Coolbots7/development-boards/atmega32u4_dev_board/images/layout/top_filled.png

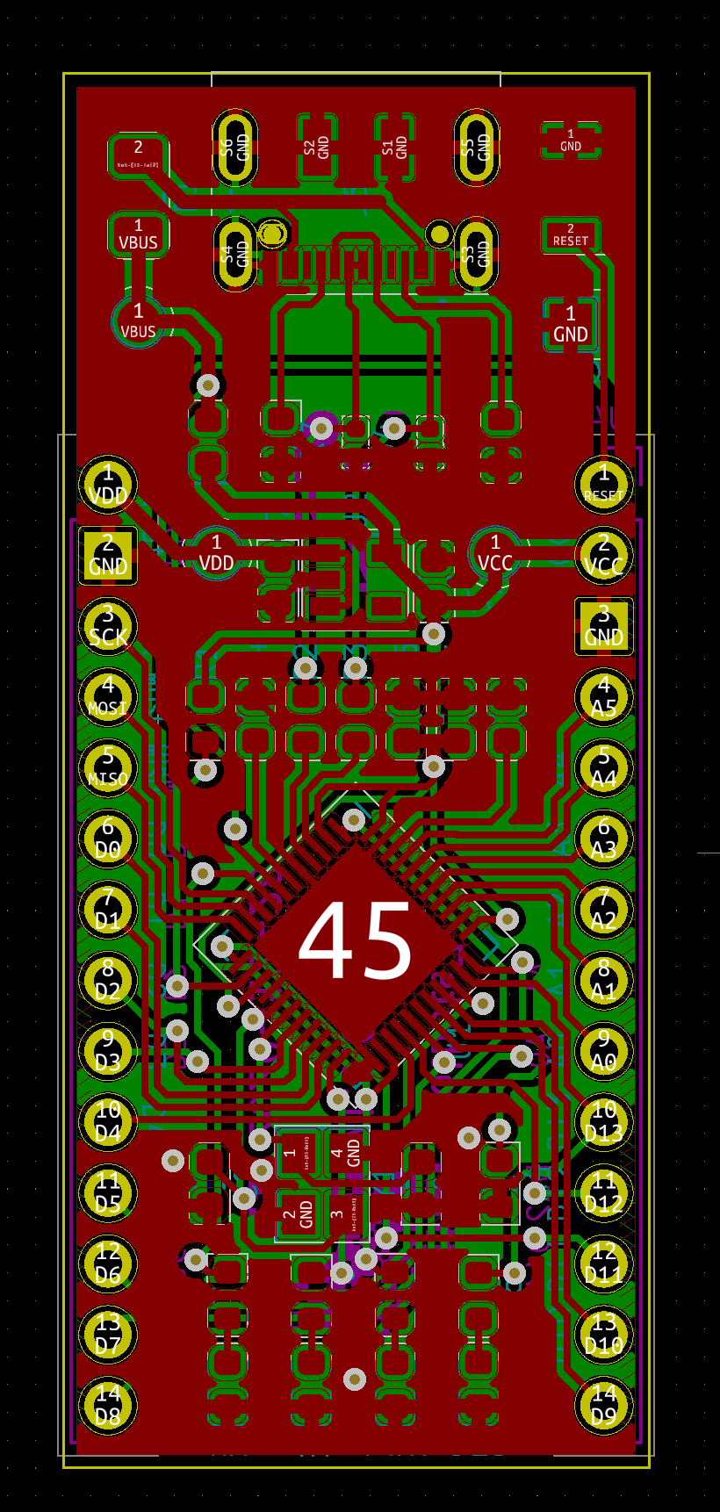
atmega32u4_dev_board/images/layout/top_filled.png
