Coolbots7/development-boards/atmega32u4_dev_board/images/layout/top_unfilled.png

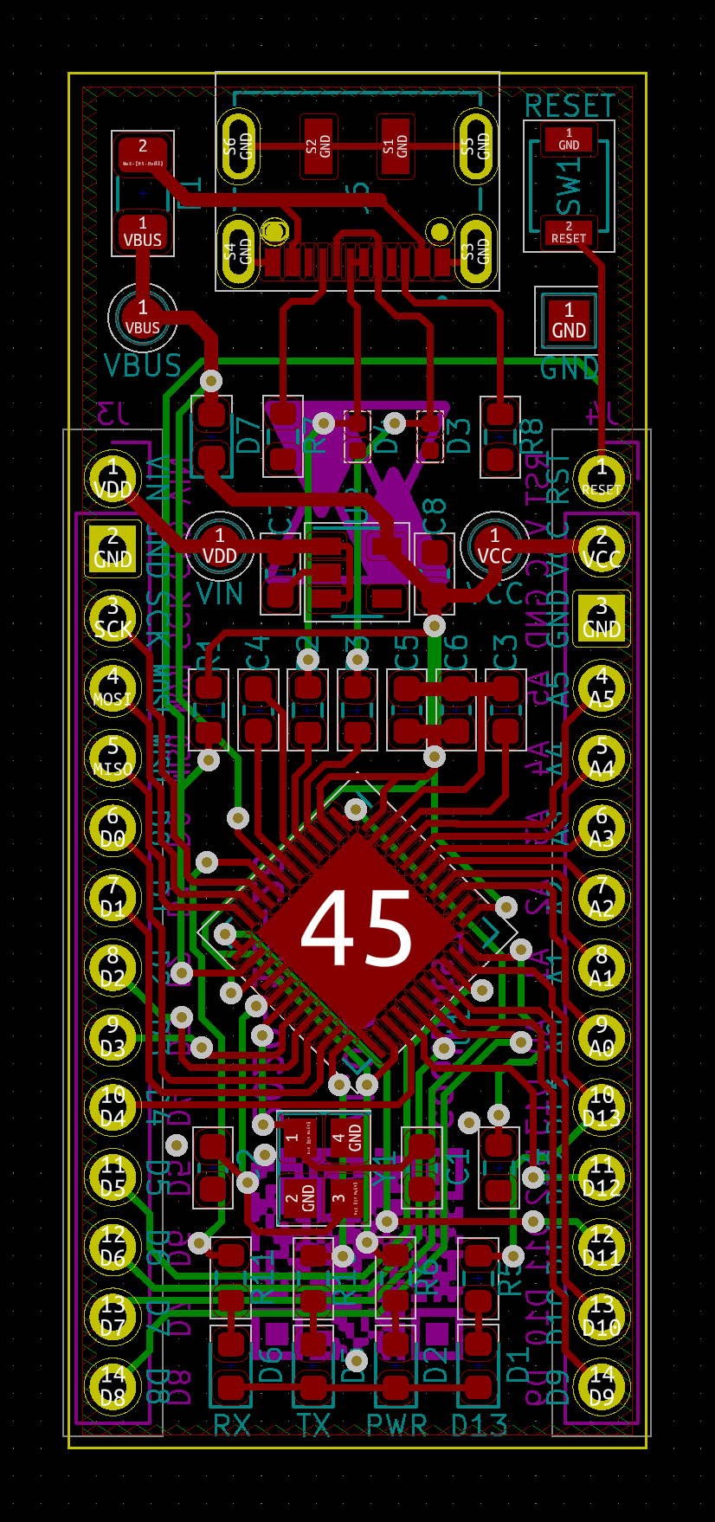
atmega32u4_dev_board/images/layout/top_unfilled.png
