Coolbots7/development-boards/atmega32u4_dev_board/images/pcb/bare/IMG_0310.jpg

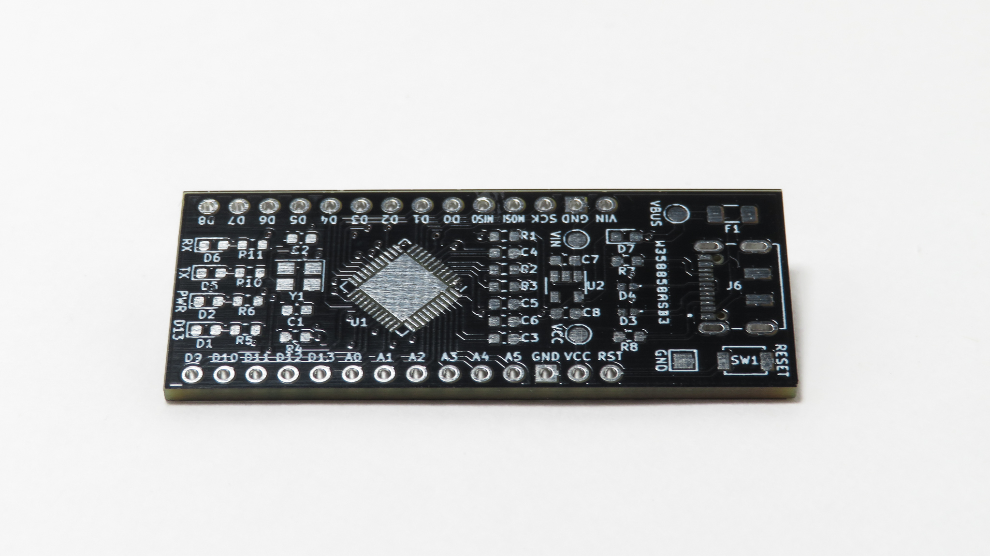
atmega32u4_dev_board/images/pcb/bare/IMG_0310.jpg
