Coolbots7/development-boards/atmega32u4_dev_board/images/pcb/headers/IMG_0332.jpg

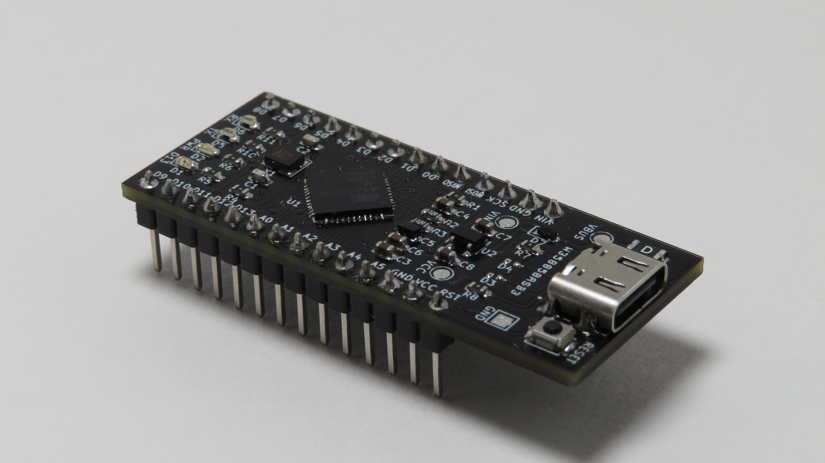
atmega32u4_dev_board/images/pcb/headers/IMG_0332.jpg
