Coolbots7/development-boards/atmega32u4_dev_board/images/pcb/populated/IMG_0331.jpg

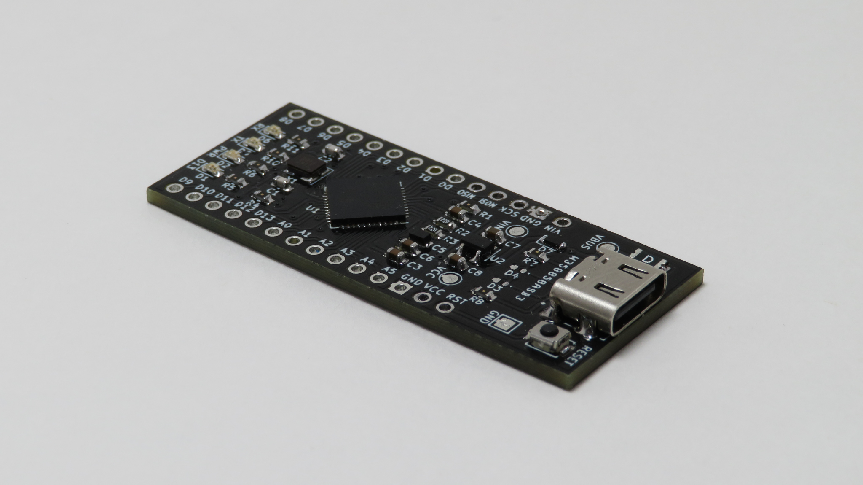
atmega32u4_dev_board/images/pcb/populated/IMG_0331.jpg
